sammothxc/clackpaq-mechanical-keyboard/pcb/clackpaq-compatible/clackpaq-compatible.kicad_sch

## KiCad design pcb/clackpaq-compatible/clackpaq-compatible.kicad_sch (2026-03-12)

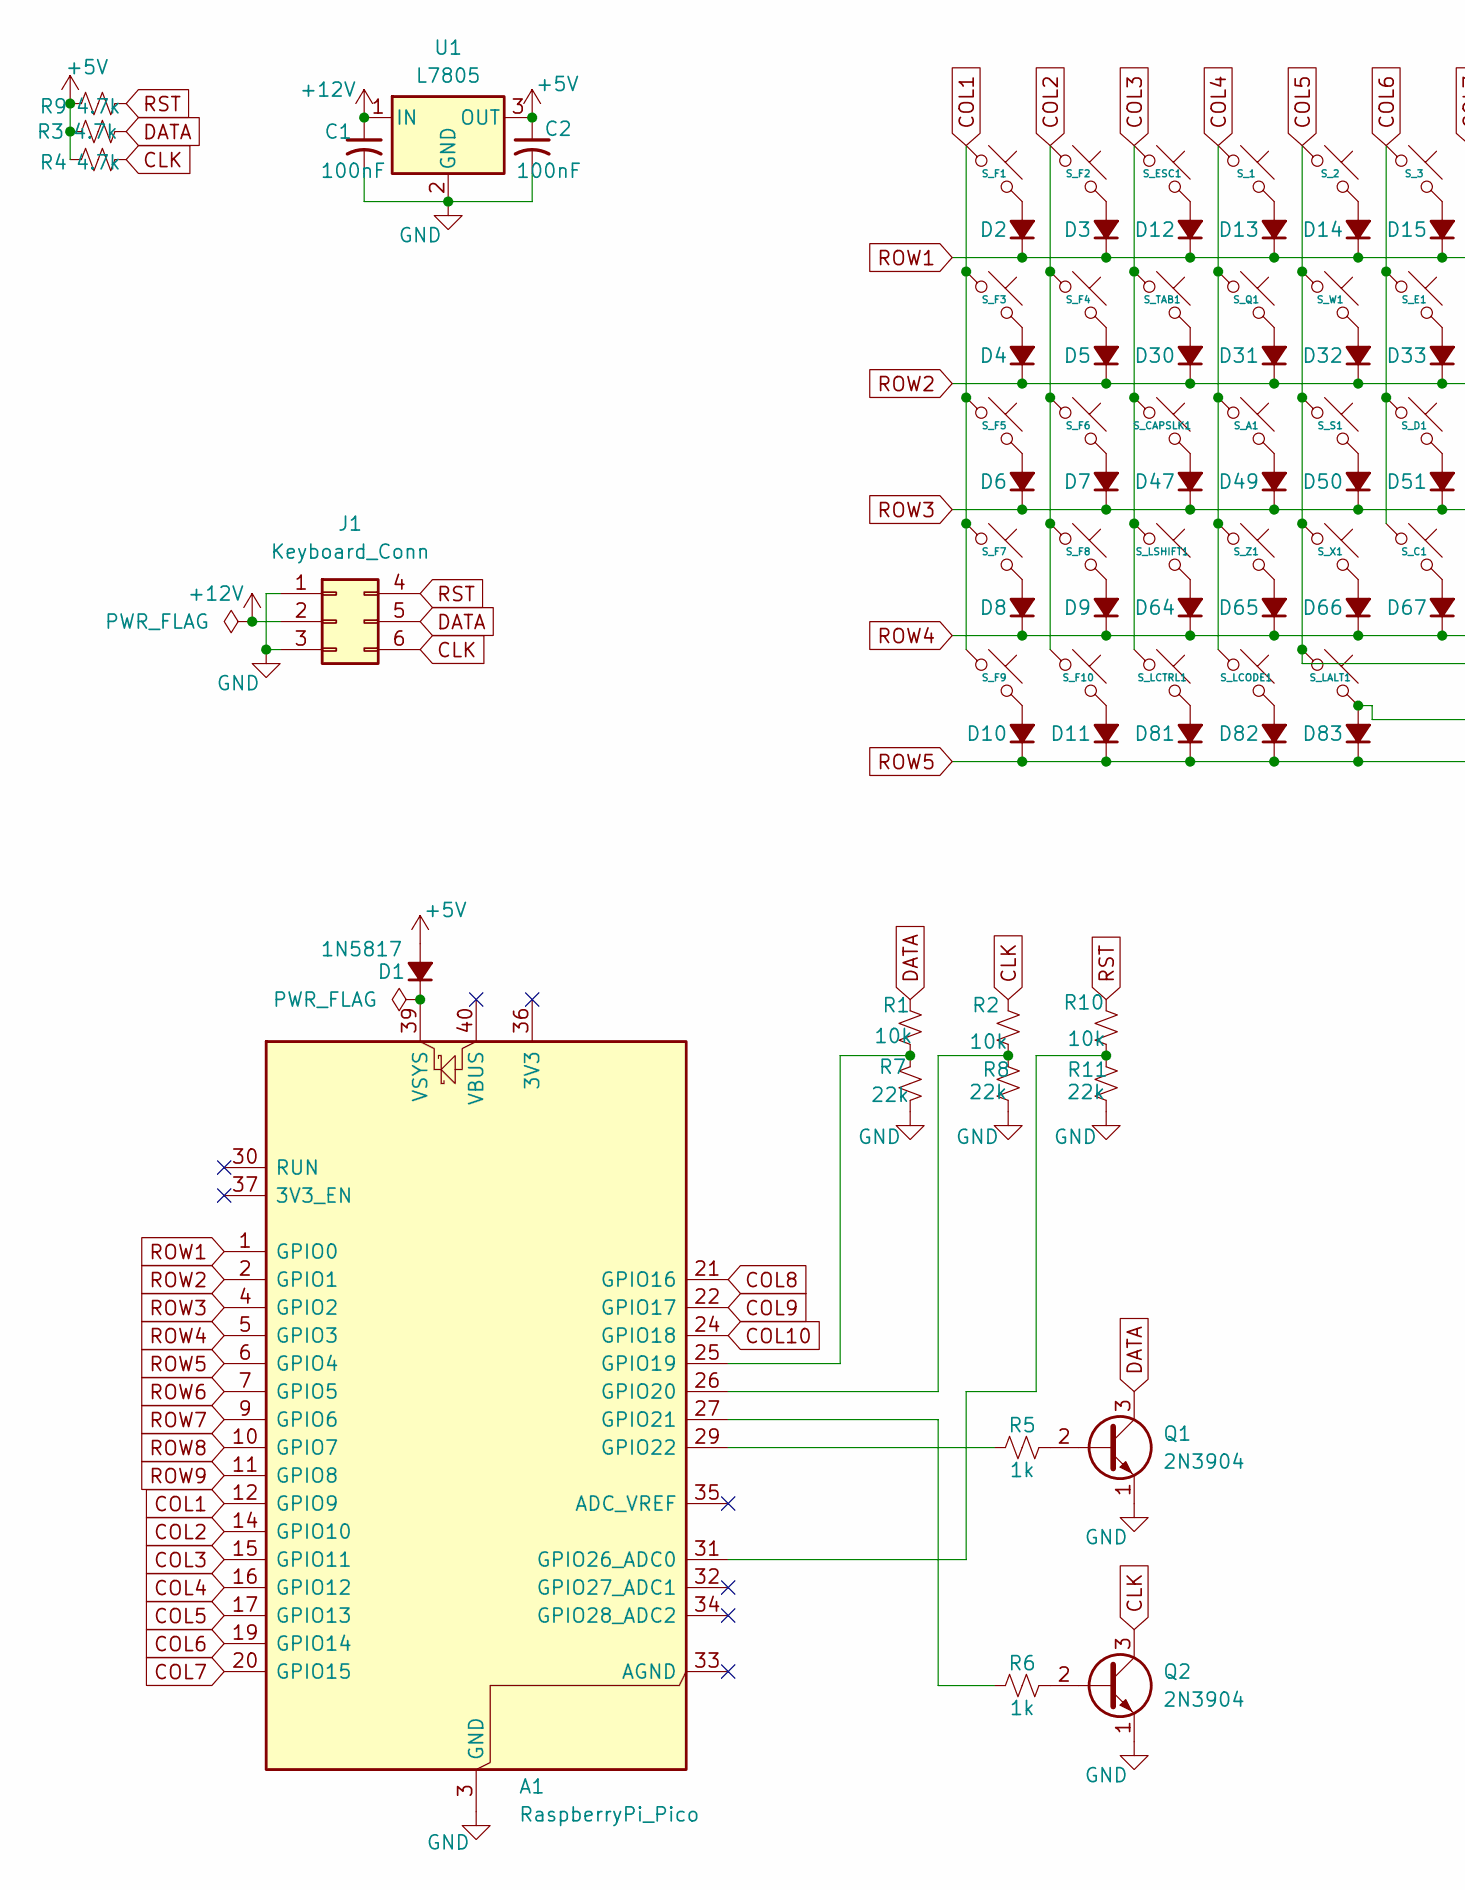
[picture p4: schematic clackpaq-compatible.kicad_sch, part in row 1, column 1]

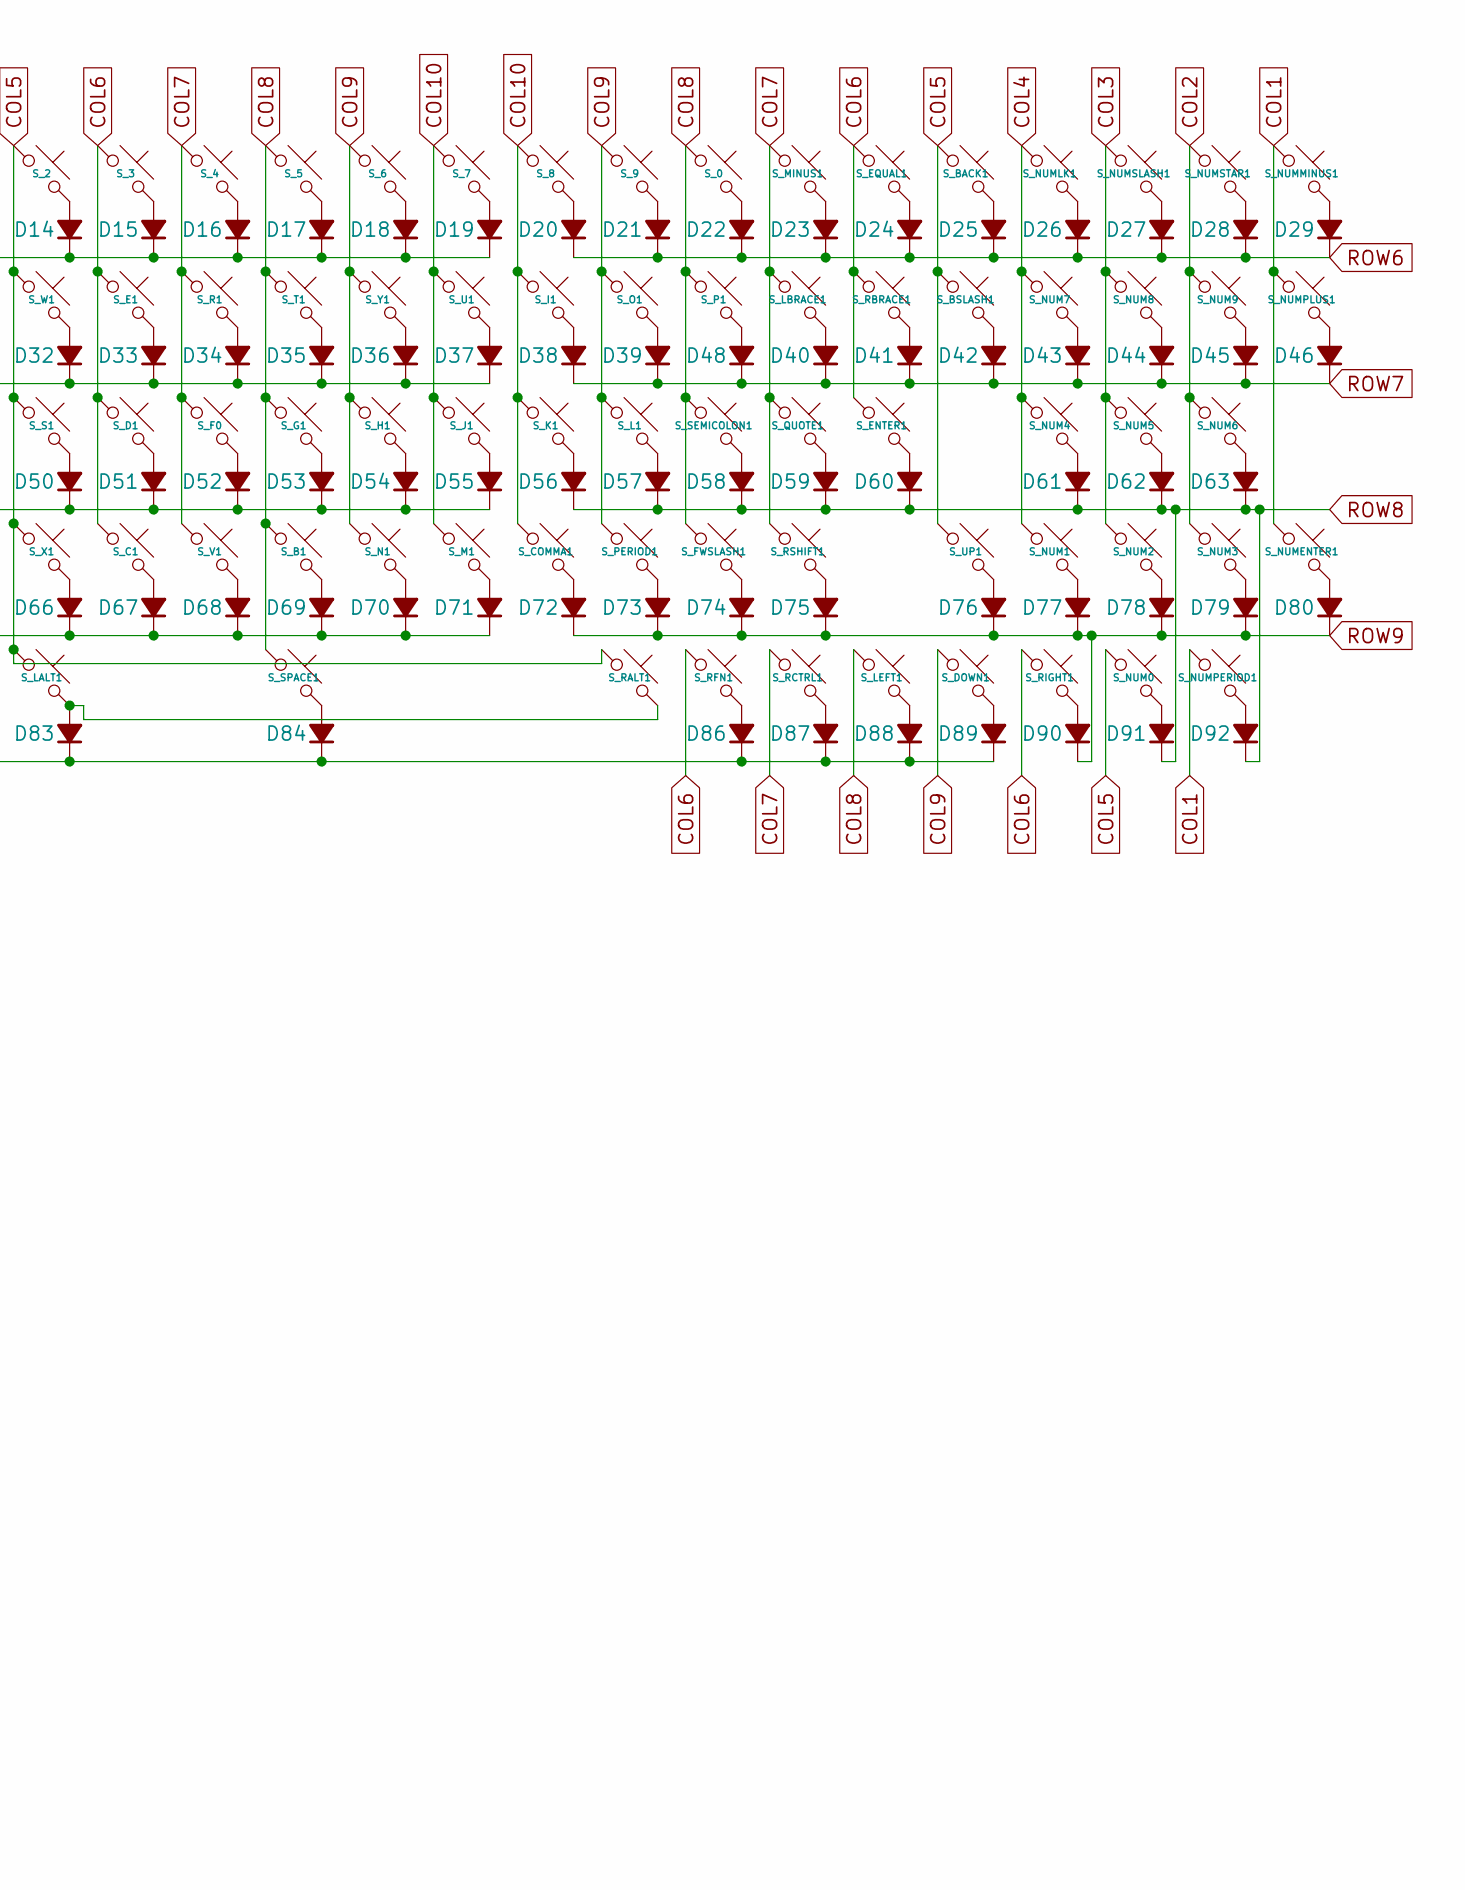
[picture p5: schematic clackpaq-compatible.kicad_sch, part in row 1, column 2]

Parts:
A1: RaspberryPi_Pico; RaspberryPi_Pico_Common_Unspecified
C1, C2: 100nF
D1: 1N5817
D2, D3, D4, D5, D6, D7, D8, D9, D10, D11, D12, D13, D14, D15, D16, D17, D18, D19, D20, D21, D22, D23, D24, D25, D26, D27, D28, D29, D30, D31, D32, D33, D34, D35, D36, D37, D38, D39, D40, D41, D42, D43, D44, D45, D46, D47, D48, D49, D50, D51, D52, D53, D54, D55, D56, D57, D58, D59, D60, D61, D62, D63, D64, D65, D66, D67, D68, D69, D70, D71, D72, D73, D74, D75, D76, D77, D78, D79, D80, D81, D82, D83, D84, D86, D87, D88, D89, D90, D91, D92: 1N4148
J1: Keyboard_Conn
Q1, Q2: 2N3904; TO-92_Inline
R1, R2, R10: 10k
R3, R4, R9: 4.7k
R5, R6: 1k
R7, R8, R11: 22k
S_0, S_1, S_2, S_3, S_4, S_5, S_6, S_7, S_8, S_9: (no value)
S_A1: (no value)
S_B1: (no value)
S_BACK1: (no value)
S_BSLASH1: (no value)
S_C1: (no value)
S_CAPSLK1: (no value)
S_COMMA1: (no value)
S_D1: (no value)
S_DOWN1: (no value)
S_E1: (no value)
S_ENTER1: (no value)
S_EQUAL1: (no value)
S_ESC1: (no value)
S_F0, S_F1, S_F2, S_F3, S_F4, S_F5, S_F6, S_F7, S_F8, S_F9, S_F10: (no value)
S_FWSLASH1: (no value)
S_G1: (no value)
S_H1: (no value)
S_I1: (no value)
S_J1: (no value)
S_K1: (no value)
S_L1: (no value)
S_LALT1: (no value)
S_LBRACE1: (no value)
S_LCODE1: (no value)
S_LCTRL1: (no value)
S_LEFT1: (no value)
S_LSHIFT1: (no value)
S_M1: (no value)
S_MINUS1: (no value)
S_N1: (no value)
S_NUM0, S_NUM1, S_NUM2, S_NUM3, S_NUM4, S_NUM5, S_NUM6, S_NUM7, S_NUM8, S_NUM9: (no value)
S_NUMENTER1: (no value)
S_NUMLK1: (no value)
S_NUMMINUS1: (no value)
S_NUMPERIOD1: (no value)
S_NUMPLUS1: (no value)
S_NUMSLASH1: (no value)
S_NUMSTAR1: (no value)
S_O1: (no value)
S_P1: (no value)
S_PERIOD1: (no value)
S_Q1: (no value)
S_QUOTE1: (no value)
S_R1: (no value)
S_RALT1: (no value)
S_RBRACE1: (no value)
S_RCTRL1: (no value)
S_RFN1: (no value)
S_RIGHT1: (no value)
S_RSHIFT1: (no value)
S_S1: (no value)
S_SEMICOLON1: (no value)
S_SPACE1: (no value)
S_T1: (no value)
S_TAB1: (no value)
S_U1: (no value)
S_UP1: (no value)
S_V1: (no value)
S_W1: (no value)
S_X1: (no value)
S_Y1: (no value)
S_Z1: (no value)
U1: L7805

Connections:
+5V: C2.1, D1.2 (A), R3.1, R4.2, R9.2, U1.3 (OUT)
+12V: C1.1, J1.2, U1.1 (IN)
CLK: J1.6, Q2.3 (C), R2.2, R4.1
COL1: A1.12 (GPIO9), S_F1.1, S_F3.1, S_F5.1, S_F7.1, S_F9.1, S_NUMENTER1.1, S_NUMMINUS1.1, S_NUMPERIOD1.1, S_NUMPLUS1.1
COL2: A1.14 (GPIO10), S_F2.1, S_F4.1, S_F6.1, S_F8.1, S_F10.1, S_NUM3.1, S_NUM6.1, S_NUM9.1, S_NUMSTAR1.1
COL3: A1.15 (GPIO11), S_CAPSLK1.1, S_ESC1.1, S_LCTRL1.1, S_LSHIFT1.1, S_NUM2.1, S_NUM5.1, S_NUM8.1, S_NUMSLASH1.1, S_TAB1.1
COL4: A1.16 (GPIO12), S_1.1, S_A1.1, S_LCODE1.1, S_NUM1.1, S_NUM4.1, S_NUM7.1, S_NUMLK1.1, S_Q1.1, S_Z1.1
COL5: A1.17 (GPIO13), S_2.1, S_BACK1.1, S_BSLASH1.1, S_LALT1.1, S_NUM0.1, S_RALT1.1, S_S1.1, S_UP1.1, S_W1.1, S_X1.1
COL6: A1.19 (GPIO14), S_3.1, S_C1.1, S_D1.1, S_E1.1, S_ENTER1.1, S_EQUAL1.1, S_RBRACE1.1, S_RFN1.1, S_RIGHT1.1
COL7: A1.20 (GPIO15), S_4.1, S_F0.1, S_LBRACE1.1, S_MINUS1.1, S_QUOTE1.1, S_R1.1, S_RCTRL1.1, S_RSHIFT1.1, S_V1.1
COL8: A1.21 (GPIO16), S_0.1, S_5.1, S_B1.1, S_FWSLASH1.1, S_G1.1, S_LEFT1.1, S_P1.1, S_SEMICOLON1.1, S_SPACE1.1, S_T1.1
COL9: A1.22 (GPIO17), S_6.1, S_9.1, S_DOWN1.1, S_H1.1, S_L1.1, S_N1.1, S_O1.1, S_PERIOD1.1, S_Y1.1
COL10: A1.24 (GPIO18), S_7.1, S_8.1, S_COMMA1.1, S_I1.1, S_J1.1, S_K1.1, S_M1.1, S_U1.1
DATA: J1.5, Q1.3 (C), R1.2, R3.2
GND: A1.3 (GND), A1.8 (GND), A1.13 (GND), A1.18 (GND), A1.23 (GND), A1.28 (GND), A1.38 (GND), C1.2, C2.2, J1.1, J1.3, Q1.1 (E), Q2.1 (E), R7.2, R8.2, R11.2, U1.2 (GND)
unnamed: A1.25 (GPIO19), R1.1, R7.1
unnamed: A1.26 (GPIO20), R2.1, R8.1
unnamed: A1.27 (GPIO21), R6.1
unnamed: A1.29 (GPIO22), R5.1
unnamed: A1.31 (GPIO26_ADC0), R10.1, R11.1
unnamed: A1.39 (VSYS), D1.1 (K)
unnamed: D2.2 (A), S_F1.2
unnamed: D3.2 (A), S_F2.2
unnamed: D4.2 (A), S_F3.2
unnamed: D5.2 (A), S_F4.2
unnamed: D6.2 (A), S_F5.2
unnamed: D7.2 (A), S_F6.2
unnamed: D8.2 (A), S_F7.2
unnamed: D9.2 (A), S_F8.2
unnamed: D10.2 (A), S_F9.2
unnamed: D11.2 (A), S_F10.2
unnamed: D12.2 (A), S_ESC1.2
unnamed: D13.2 (A), S_1.2
unnamed: D14.2 (A), S_2.2
unnamed: D15.2 (A), S_3.2
unnamed: D16.2 (A), S_4.2
unnamed: D17.2 (A), S_5.2
unnamed: D18.2 (A), S_6.2
unnamed: D19.2 (A), S_7.2
unnamed: D20.2 (A), S_8.2
unnamed: D21.2 (A), S_9.2
unnamed: D22.2 (A), S_0.2
unnamed: D23.2 (A), S_MINUS1.2
unnamed: D24.2 (A), S_EQUAL1.2
unnamed: D25.2 (A), S_BACK1.2
unnamed: D26.2 (A), S_NUMLK1.2
unnamed: D27.2 (A), S_NUMSLASH1.2
unnamed: D28.2 (A), S_NUMSTAR1.2
unnamed: D29.2 (A), S_NUMMINUS1.2
unnamed: D30.2 (A), S_TAB1.2
unnamed: D31.2 (A), S_Q1.2
unnamed: D32.2 (A), S_W1.2
unnamed: D33.2 (A), S_E1.2
unnamed: D34.2 (A), S_R1.2
unnamed: D35.2 (A), S_T1.2
unnamed: D36.2 (A), S_Y1.2
unnamed: D37.2 (A), S_U1.2
unnamed: D38.2 (A), S_I1.2
unnamed: D39.2 (A), S_O1.2
unnamed: D40.2 (A), S_LBRACE1.2
unnamed: D41.2 (A), S_RBRACE1.2
unnamed: D42.2 (A), S_BSLASH1.2
unnamed: D43.2 (A), S_NUM7.2
unnamed: D44.2 (A), S_NUM8.2
unnamed: D45.2 (A), S_NUM9.2
unnamed: D46.2 (A), S_NUMPLUS1.2
unnamed: D47.2 (A), S_CAPSLK1.2
unnamed: D48.2 (A), S_P1.2
unnamed: D49.2 (A), S_A1.2
unnamed: D50.2 (A), S_S1.2
unnamed: D51.2 (A), S_D1.2
unnamed: D52.2 (A), S_F0.2
unnamed: D53.2 (A), S_G1.2
unnamed: D54.2 (A), S_H1.2
unnamed: D55.2 (A), S_J1.2
unnamed: D56.2 (A), S_K1.2
unnamed: D57.2 (A), S_L1.2
unnamed: D58.2 (A), S_SEMICOLON1.2
unnamed: D59.2 (A), S_QUOTE1.2
unnamed: D60.2 (A), S_ENTER1.2
unnamed: D61.2 (A), S_NUM4.2
unnamed: D62.2 (A), S_NUM5.2
unnamed: D63.2 (A), S_NUM6.2
unnamed: D64.2 (A), S_LSHIFT1.2
unnamed: D65.2 (A), S_Z1.2
unnamed: D66.2 (A), S_X1.2
unnamed: D67.2 (A), S_C1.2
unnamed: D68.2 (A), S_V1.2
unnamed: D69.2 (A), S_B1.2
unnamed: D70.2 (A), S_N1.2
unnamed: D71.2 (A), S_M1.2
unnamed: D72.2 (A), S_COMMA1.2
unnamed: D73.2 (A), S_PERIOD1.2
unnamed: D74.2 (A), S_FWSLASH1.2
unnamed: D75.2 (A), S_RSHIFT1.2
unnamed: D76.2 (A), S_UP1.2
unnamed: D77.2 (A), S_NUM1.2
unnamed: D78.2 (A), S_NUM2.2
unnamed: D79.2 (A), S_NUM3.2
unnamed: D80.2 (A), S_NUMENTER1.2
unnamed: D81.2 (A), S_LCTRL1.2
unnamed: D82.2 (A), S_LCODE1.2
unnamed: D83.2 (A), S_LALT1.2, S_RALT1.2
unnamed: D84.2 (A), S_SPACE1.2
unnamed: D86.2 (A), S_RFN1.2
unnamed: D87.2 (A), S_RCTRL1.2
unnamed: D88.2 (A), S_LEFT1.2
unnamed: D89.2 (A), S_DOWN1.2
unnamed: D90.2 (A), S_RIGHT1.2
unnamed: D91.2 (A), S_NUM0.2
unnamed: D92.2 (A), S_NUMPERIOD1.2
unnamed: Q1.2 (B), R5.2
unnamed: Q2.2 (B), R6.2
ROW1: A1.1 (GPIO0), D2.1 (K), D3.1 (K), D12.1 (K), D13.1 (K), D14.1 (K), D15.1 (K), D16.1 (K), D17.1 (K), D18.1 (K), D19.1 (K)
ROW2: A1.2 (GPIO1), D4.1 (K), D5.1 (K), D30.1 (K), D31.1 (K), D32.1 (K), D33.1 (K), D34.1 (K), D35.1 (K), D36.1 (K), D37.1 (K)
ROW3: A1.4 (GPIO2), D6.1 (K), D7.1 (K), D47.1 (K), D49.1 (K), D50.1 (K), D51.1 (K), D52.1 (K), D53.1 (K), D54.1 (K), D55.1 (K)
ROW4: A1.5 (GPIO3), D8.1 (K), D9.1 (K), D64.1 (K), D65.1 (K), D66.1 (K), D67.1 (K), D68.1 (K), D69.1 (K), D70.1 (K), D71.1 (K)
ROW5: A1.6 (GPIO4), D10.1 (K), D11.1 (K), D81.1 (K), D82.1 (K), D83.1 (K), D84.1 (K), D86.1 (K), D87.1 (K), D88.1 (K), D89.1 (K)
ROW6: A1.7 (GPIO5), D20.1 (K), D21.1 (K), D22.1 (K), D23.1 (K), D24.1 (K), D25.1 (K), D26.1 (K), D27.1 (K), D28.1 (K), D29.1 (K)
ROW7: A1.9 (GPIO6), D38.1 (K), D39.1 (K), D40.1 (K), D41.1 (K), D42.1 (K), D43.1 (K), D44.1 (K), D45.1 (K), D46.1 (K), D48.1 (K)
ROW8: A1.10 (GPIO7), D56.1 (K), D57.1 (K), D58.1 (K), D59.1 (K), D60.1 (K), D61.1 (K), D62.1 (K), D63.1 (K), D91.1 (K), D92.1 (K)
ROW9: A1.11 (GPIO8), D72.1 (K), D73.1 (K), D74.1 (K), D75.1 (K), D76.1 (K), D77.1 (K), D78.1 (K), D79.1 (K), D80.1 (K), D90.1 (K)
RST: J1.4, R9.1, R10.2
